tharejarehan0-a11y/Keypad/3D_Models/STL/assembly/Assembly_Components/Assembly 1 - Diode_DO-35_6.stl

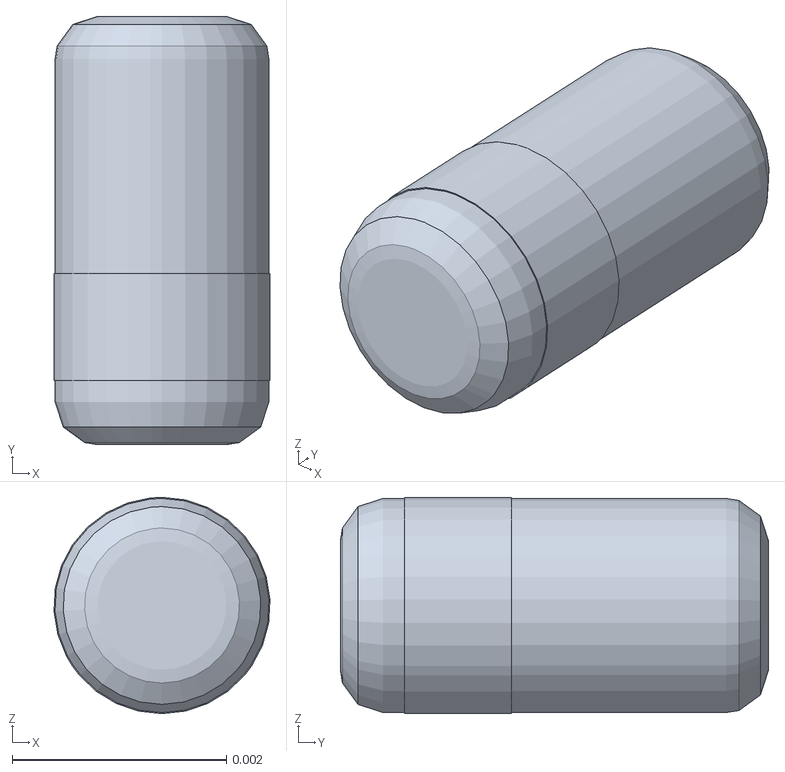
[picture p15: CAD file, 2026-06-01]
3D_Models/STL/assembly/Assembly_Components/Assembly 1 - Diode_DO-35_6.stl
0.00202 x 0.004 x 0.00202
