tharejarehan0-a11y/Keypad/3D_Models/STL/assembly/Assembly_Components/Assembly 1 - mech_Keyboard_pad (17).stl

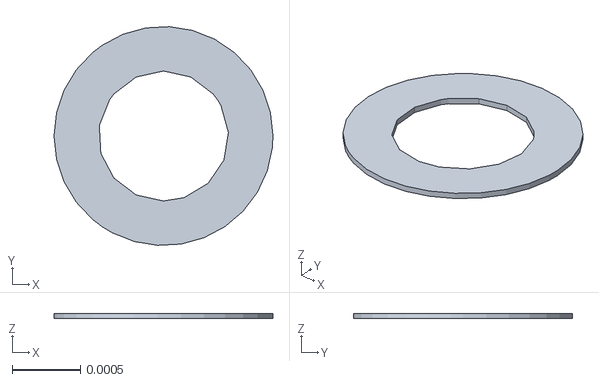
[picture p16: CAD file, 2026-06-01]
3D_Models/STL/assembly/Assembly_Components/Assembly 1 - mech_Keyboard_pad (17).stl
0.0016 x 0.0016 x 4e-05
