tharejarehan0-a11y/Keypad/3D_Models/STL/assembly/Assembly_Components/Assembly 1 - mech_Keyboard_pad (31).stl

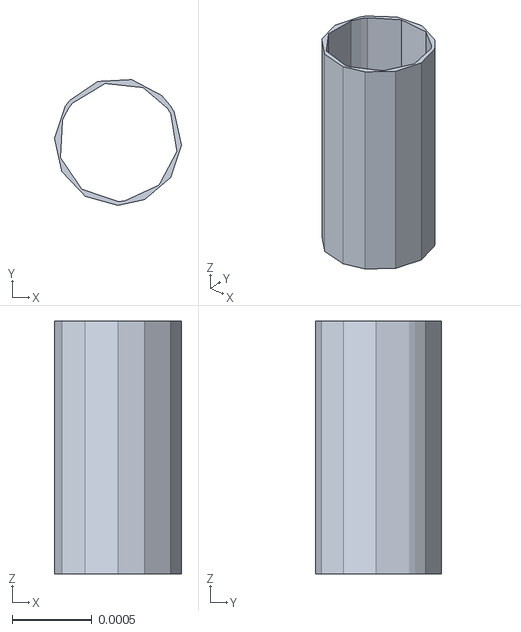
[picture p17: CAD file, 2026-06-01]
3D_Models/STL/assembly/Assembly_Components/Assembly 1 - mech_Keyboard_pad (31).stl
0.000799 x 0.000791 x 0.00159
