tharejarehan0-a11y/Keypad/3D_Models/STL/assembly/Assembly_Components/Assembly 1 - mech_Keyboard_copper (117).stl

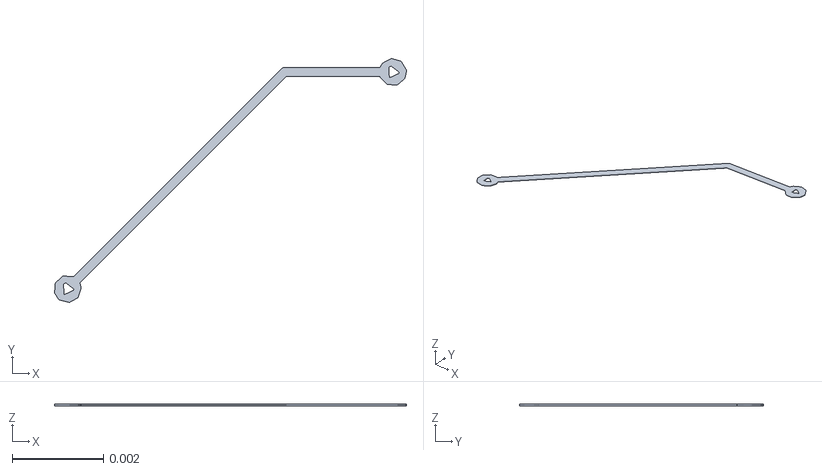
[picture p18: CAD file, 2026-06-01]
3D_Models/STL/assembly/Assembly_Components/Assembly 1 - mech_Keyboard_copper (117).stl
0.00773 x 0.00536 x 3.5e-05
