tharejarehan0-a11y/Keypad/3D_Models/STL/assembly/Assembly_Components/Assembly 1 - Diode_DO-35_4.stl

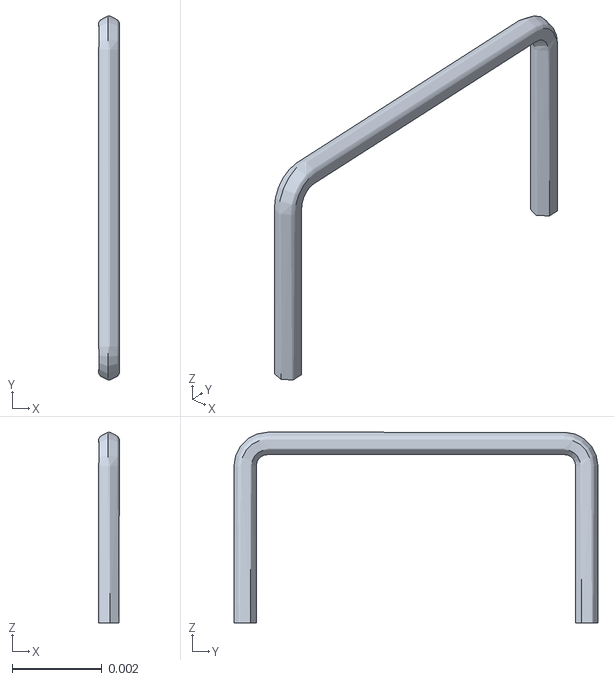
[picture p19: CAD file, 2026-06-01]
3D_Models/STL/assembly/Assembly_Components/Assembly 1 - Diode_DO-35_4.stl
0.000464 x 0.00812 x 0.00425
