tharejarehan0-a11y/Keypad/3D_Models/STL/assembly/Assembly_Components/Assembly 1 - mech_Keyboard_copper (115).stl

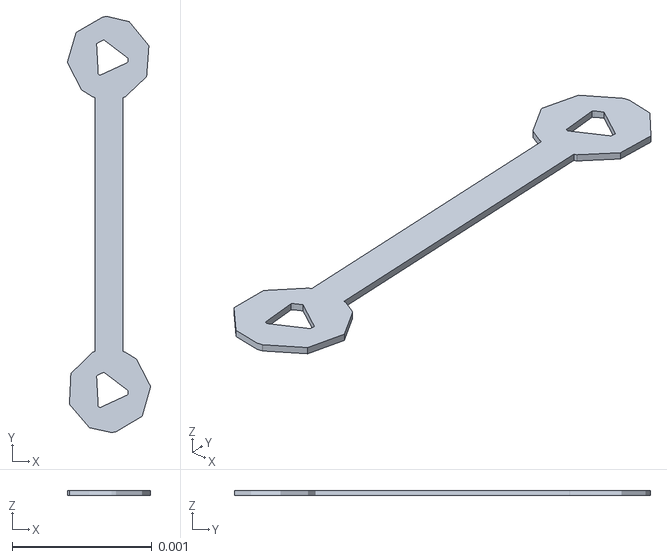
[picture p20: CAD file, 2026-06-01]
3D_Models/STL/assembly/Assembly_Components/Assembly 1 - mech_Keyboard_copper (115).stl
0.000597 x 0.00298 x 3.5e-05
