tharejarehan0-a11y/Keypad/3D_Models/STL/assembly/Assembly_Components/Assembly 1 - mech_Keyboard_pad (254).stl

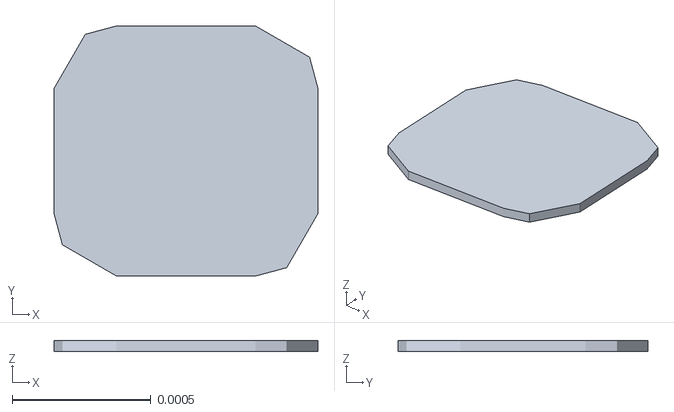
[picture p21: CAD file, 2026-06-01]
3D_Models/STL/assembly/Assembly_Components/Assembly 1 - mech_Keyboard_pad (254).stl
0.00095 x 0.0009 x 4e-05
