tharejarehan0-a11y/Keypad/3D_Models/STL/assembly/Assembly_Components/Assembly 1 - 1x1 R1 v23.stl

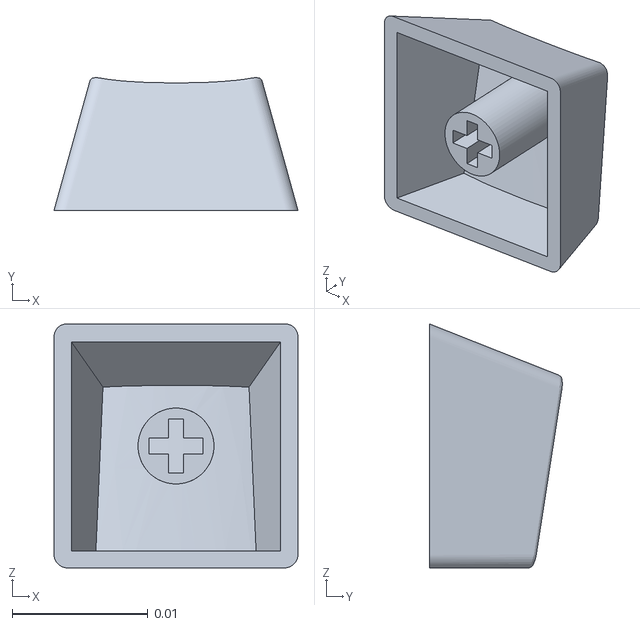
[picture p24: CAD file, 2026-06-01]
3D_Models/STL/assembly/Assembly_Components/Assembly 1 - 1x1 R1 v23.stl
0.018 x 0.00978 x 0.018
