tharejarehan0-a11y/Keypad/3D_Models/STL/assembly/Assembly_Components/Assembly 1 - MX_PCB_7.stl

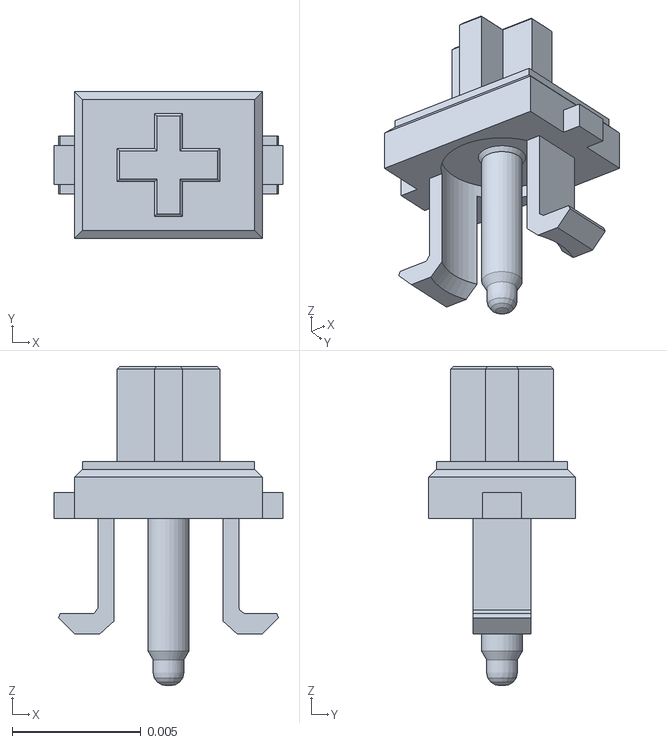
[picture p25: CAD file, 2026-06-01]
3D_Models/STL/assembly/Assembly_Components/Assembly 1 - MX_PCB_7.stl
0.0089 x 0.0057 x 0.0124
