tharejarehan0-a11y/Keypad/3D_Models/STL/assembly/Assembly_Components/Assembly 1 - RaspberryPi_Pico_Module_KiCad.stl

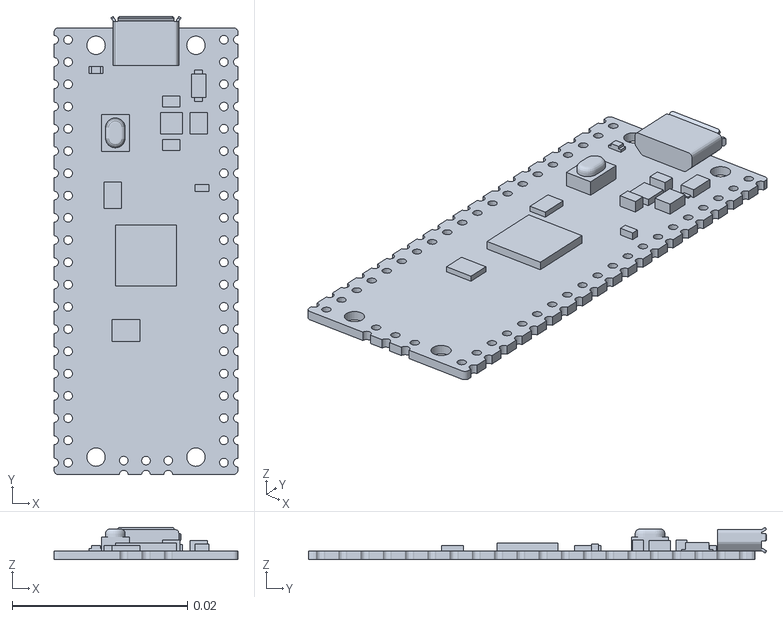
[picture p40: CAD file, 2026-06-01]
3D_Models/STL/assembly/Assembly_Components/Assembly 1 - RaspberryPi_Pico_Module_KiCad.stl
0.021 x 0.0523 x 0.0037
